Nishida-Lab/forest_robot_project/fr01_description/meshes/visual/bogie_right_link_texture.png

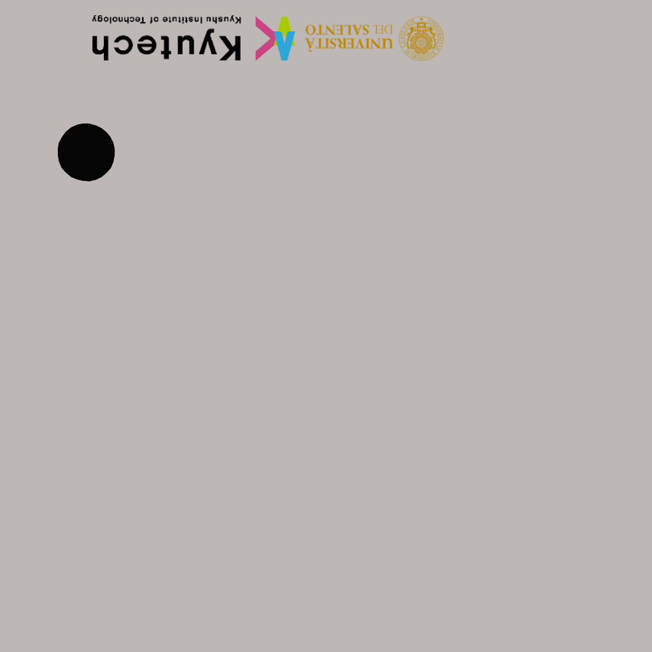
fr01_description/meshes/visual/bogie_right_link_texture.png
