Nishida-Lab/forest_robot_project/fr01_driver/config/b3m_driver.yaml

joint_0_driver:
  joint_name: joint_0
  id: 0
  min_angle: -200
  max_angle:  60

joint_1_driver:
  joint_name: joint_1
  id: 1
  min_angle: -55
  max_angle:  200

joint_2_driver:
  joint_name: joint_2
  id: 2
  min_angle: -50
  max_angle:  200

joint_3_driver:
  joint_name: joint_3
  id: 3
  min_angle: -200
  max_angle:  50
